rastocs2/AquariumController/Pics/lcd4.jpg

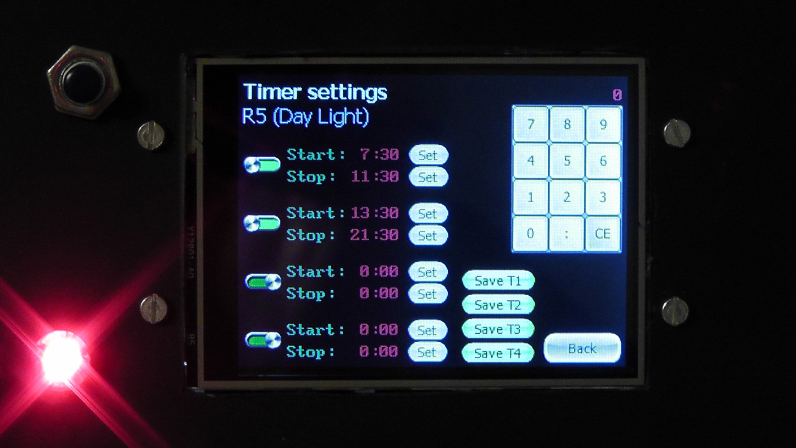
Pics/lcd4.jpg
