rastocs2/AquariumController/Pics/lcd5.jpg

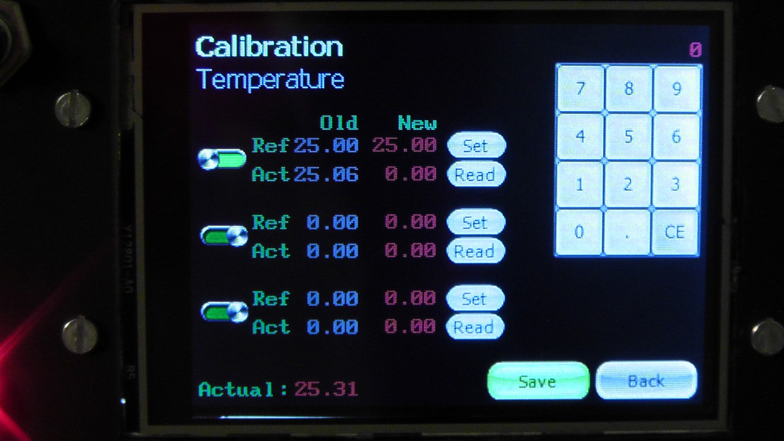
Pics/lcd5.jpg
