rastocs2/AquariumController/Pics/power1.jpg

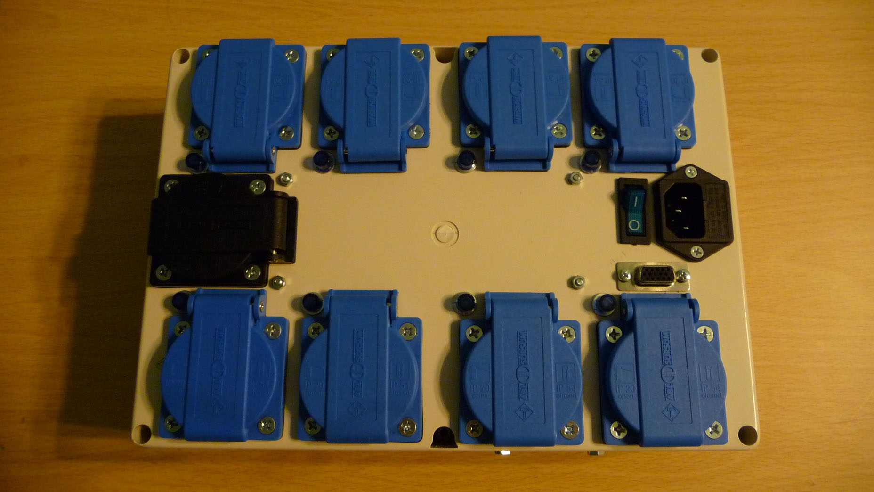
Pics/power1.jpg
