rastocs2/AquariumController/Pics/power3.jpg

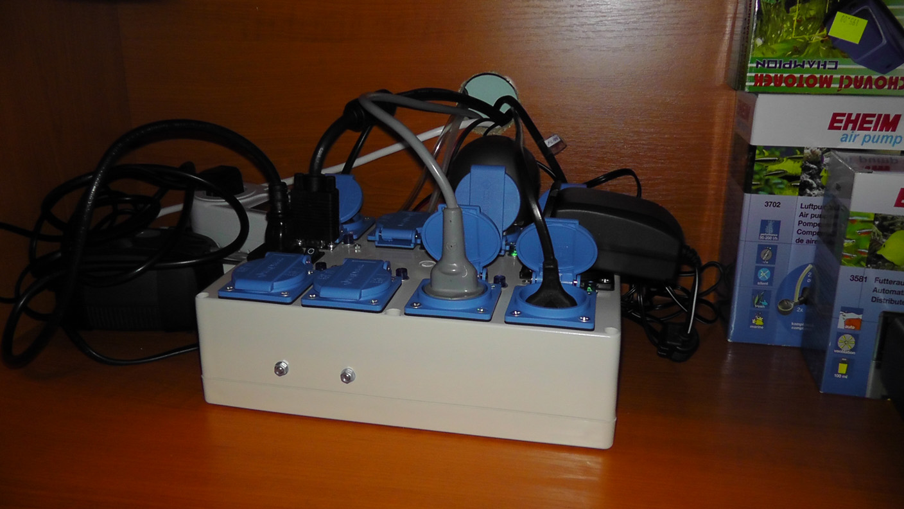
Pics/power3.jpg
