rastocs2/AquariumController/Pics/VisiGenie.png

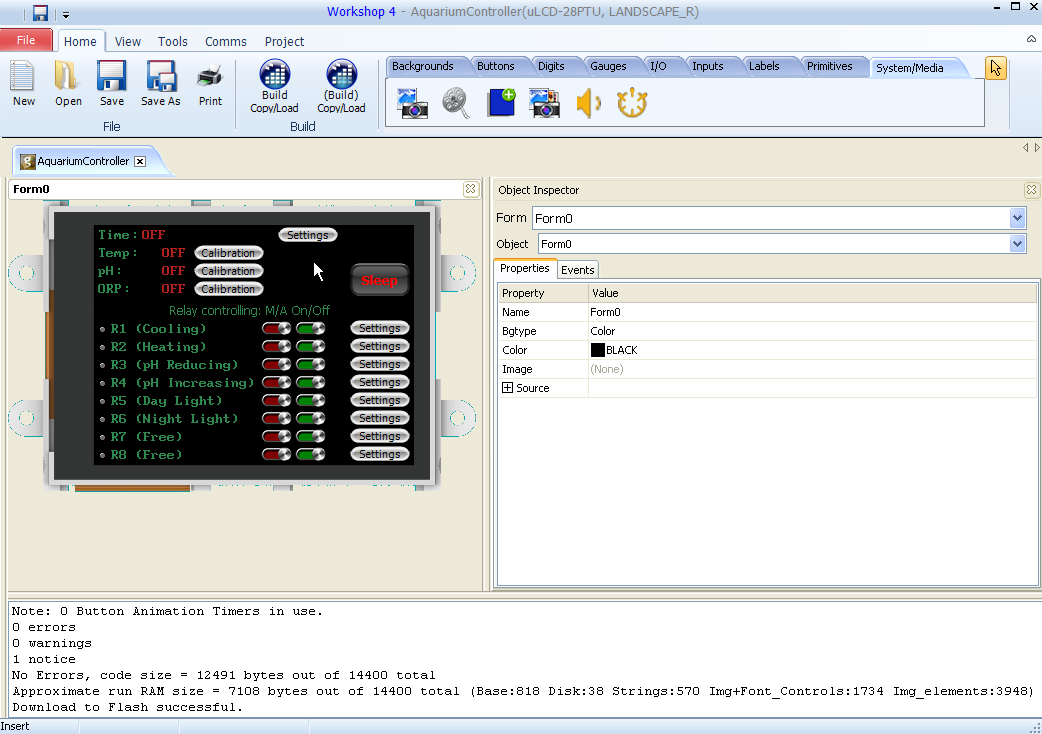
Pics/VisiGenie.png
