rastocs2/AquariumController/Arduino/AquariumController/AQUA_temp.cpp

/*
  Project: Aquarium Controller
  Library: Temperature (a 4.7K resistor is necessary)
  Version: 1.0
  Author: Rastislav Birka
*/

#include <avr/eeprom.h>
#include <Arduino.h>
#include "AQUA_temp.h"

/*
  Public Functions
*/

void AQUA_temp::init(uint8_t dqPin, uint8_t calibrate_points, uint8_t calibrate_address) {
  uint16_t value, position;
  uint8_t i;

  _dqPin = dqPin;
  _pointCount = calibrate_points;
  _calibrateAddress = calibrate_address;
  _calData = new AQUA_tempCalibrationPoint[_pointCount];
  _usedData = new AQUA_tempCalibrationPoint[_pointCount];
  _const = new float[(_pointCount - 1)*2];

  position = 0;
  for(i = 0; i < _pointCount; i++) {
    eeprom_busy_wait();
    value = eeprom_read_word((const uint16_t *)(_calibrateAddress + position));
    if(value == 0xFFFF) { //address wasn't set yet
      _calData[i].state = 0;
      _calData[i].refValue = 0;
      _calData[i].actValue = 0;
      position+= 4;
    } else {
      _calData[i].state = (bool)(value & 32768);
      if(_calData[i].state == 1) {
         value-= 32768;
      }
      _calData[i].refValue = (float)value/100.0;
      position+= 2;
      eeprom_busy_wait();
      value = eeprom_read_word((const uint16_t *)(_calibrateAddress + position));
      _calData[i].actValue = (float)value/100.0;
      position+= 2;
    }
  }
  _setCalibrationValues();
  pinMode(_dqPin, INPUT);
}

float AQUA_temp::getTemp(bool calibrate) {
  uint8_t lowByte, highByte;
  int16_t rawTemp;
  float res = 0;

  _reset();
  _write(DS18B20_SKIPROM);
  _write(DS18B20_CONVERTTEMP);
  _wait_to_convert();
  _reset();
  _write(DS18B20_SKIPROM);
  _write(DS18B20_RSCRATCHPAD);
  lowByte = _read();
  highByte = _read();
  _reset();

  rawTemp = (((int16_t)highByte) << 8) | lowByte;
  res = (float)rawTemp * 0.0625;
  if(calibrate == 0) {
    if(_usedPoints == 1) {
      res+= _const[0];
    } else if(_usedPoints > 1) {
      if(res >= _usedData[_usedPoints-1].actValue) {
        res = _const[(_usedPoints-2)*2]*res + _const[(_usedPoints-2)*2 + 1];
      } else {
        for(uint8_t i = 1; i < _usedPoints; i++) {
          if(res <= _usedData[i].actValue) {
            res = _const[(i-1)*2]*res + _const[(i-1)*2 + 1];
            break;
          }
        }
      }
    }
  }

  return res;
}

bool AQUA_temp::calibration(uint8_t point, AQUA_tempCalibrationPoint *values) {
  bool res = false;

  if(point < _pointCount && point >= 0 && values->refValue <= 4999 && values->refValue >= 0 && values->actValue <= 4999 && values->actValue >= 0) {
    if(values->state != _calData[point].state || values->refValue != _calData[point].refValue || values->actValue != _calData[point].actValue) {
      _calData[point].state = values->state;
      _calData[point].refValue = values->refValue;
      _calData[point].actValue = values->actValue;
      uint16_t plusValue = 0;
      if(_calData[point].state == 1) {
        plusValue+= 32768;
      }
      uint16_t position = point*4;
      eeprom_busy_wait();
      eeprom_write_word((uint16_t *)(_calibrateAddress + position), _calData[point].refValue*100 + plusValue);
      position+= 2;
      eeprom_busy_wait();
      eeprom_write_word((uint16_t *)(_calibrateAddress + position), _calData[point].actValue*100);
      _setCalibrationValues();
      res = true;
    }
  }
  return res;
}

AQUA_tempCalibrationPoint AQUA_temp::readCalibrationPoint(uint8_t point) {
  AQUA_tempCalibrationPoint calPoint;
  if(point < _pointCount && point >= 0) {
    calPoint.state = _calData[point].state;
    calPoint.refValue = _calData[point].refValue;
    calPoint.actValue = _calData[point].actValue;
  } else {
    calPoint.state = 0;
    calPoint.refValue = 0;
    calPoint.actValue = 0;
  }
  return calPoint;
}

/*
  Private Functions
*/

/*
c1 = (ref2 - ref1)/(act2 - act1)
c2 = ref2 - c1*act2
temp = c1*SensorValue + c2
*/
void AQUA_temp::_setCalibrationValues() {
  uint8_t i,j;
  bool isCorrect;

  _usedPoints = 0;
  for(i = 0; i < _pointCount; i++) {
    if(_calData[i].state == 1 && _calData[i].actValue > 0 && _calData[i].refValue > 0) {
      if(_usedPoints > 0) {
        isCorrect = 1;
        for(j = 0; j < _usedPoints; j++) {
          if(_calData[i].actValue == _usedData[j].actValue || _calData[i].refValue == _usedData[j].refValue) {
            isCorrect = 0;
            break;
          }
        }
        if(isCorrect == 1) {
          j = _usedPoints;
          for(j; j > 0 && _usedData[j-1].actValue > _calData[i].actValue; --j) {
            _usedData[j].state = _usedData[j-1].state;
            _usedData[j].refValue = _usedData[j-1].refValue;
            _usedData[j].actValue = _usedData[j-1].actValue;
          }
          _usedData[j].state = _calData[i].state;
          _usedData[j].refValue = _calData[i].refValue;
          _usedData[j].actValue = _calData[i].actValue;
          _usedPoints++;
        }
      } else {
        _usedData[_usedPoints].state = _calData[i].state;
        _usedData[_usedPoints].refValue = _calData[i].refValue;
        _usedData[_usedPoints].actValue = _calData[i].actValue;
        _usedPoints++;
      }
    }
  }
  if(_usedPoints == 1) {
    _const[0] = (_usedData[0].refValue - _usedData[0].actValue);
  } else if(_usedPoints > 1) {
    for(i = 0; i < _usedPoints - 1; i++) {
      _const[i*2] = (_usedData[i+1].refValue - _usedData[i].refValue)/(_usedData[i+1].actValue - _usedData[i].actValue);
      _const[i*2 + 1] = _usedData[i+1].refValue - _const[i*2]*_usedData[i+1].actValue;
    }
  }
}

bool AQUA_temp::_reset(void) {
  bool res;

  noInterrupts();
  digitalWrite(_dqPin, HIGH);
  digitalWrite(_dqPin, LOW);
  pinMode(_dqPin, OUTPUT);
  interrupts();
  delayMicroseconds(480);
  noInterrupts();
  pinMode(_dqPin, INPUT);
  delayMicroseconds(70);
  res = !digitalRead(_dqPin);
  interrupts();
  delayMicroseconds(410);

  return res;
}

uint8_t AQUA_temp::_read(void) {
  uint8_t res = 0;

  for(uint8_t bitMask = 0x01; bitMask; bitMask <<= 1) {
    if(_read_bit()) {
      res |= bitMask;
    }
  }
  return res;
}

uint8_t AQUA_temp::_read_bit(void) {
  uint8_t res;

  noInterrupts();
  pinMode(_dqPin, OUTPUT);
  digitalWrite(_dqPin, LOW);
  delayMicroseconds(3);
  pinMode(_dqPin, INPUT);
//  digitalWrite(_dqPin, HIGH);
  delayMicroseconds(10);
  res = digitalRead(_dqPin);
  interrupts();
  delayMicroseconds(53);

  return res;
}

void AQUA_temp::_write(uint8_t command) {
  for(uint8_t bitMask = 0x01; bitMask; bitMask <<= 1) {
    _write_bit((bitMask & command)?1:0);
  }
/*  noInterrupts();
  pinMode(_dqPin, INPUT);
  digitalWrite(_dqPin, LOW);
  interrupts();*/
}

void AQUA_temp::_write_bit(uint8_t value) {
  if(value & 1) {
    noInterrupts();
    digitalWrite(_dqPin, LOW);
    pinMode(_dqPin, OUTPUT);
    delayMicroseconds(10);
    digitalWrite(_dqPin, HIGH);
    interrupts();
    delayMicroseconds(55);
  } else {
    noInterrupts();
    digitalWrite(_dqPin, LOW);
    pinMode(_dqPin, OUTPUT);
    delayMicroseconds(65);
    digitalWrite(_dqPin, HIGH);
    interrupts();
    delayMicroseconds(5);
  }
}

void AQUA_temp::_wait_to_convert(void) {
  unsigned long waiting = millis() + 750;
  while(millis() < waiting) {
    if(digitalRead(_dqPin) > 0) {
      break;
    }
  }
}
